foxieproducts/cardclock/firmware/src/characters.hpp

// This file implements characters as lines of code within display.hpp
// It is not meant to be included elsewhere.

// clang-format off
#define CHAR(c, ...) (character == c) { charData = { __VA_ARGS__ }; }
if      CHAR('A',
          0, 1, 0,
          1, 0, 1,
          1, 0, 1,
          1, 1, 1,
          1, 0, 1)
else if CHAR('B',
          1, 1, 0,
          1, 0, 1,
          1, 1, 0,
          1, 0, 1,
          1, 1, 0)
else if CHAR('C',
          0, 1, 1,
          1, 0, 0,
          1, 0, 0,
          1, 0, 0,
          0, 1, 1)
else if CHAR('D',
          1, 1, 0,
          1, 0, 1,
          1, 0, 1,
          1, 0, 1,
          1, 1, 0)
else if CHAR('E',
          1, 1, 1,
          1, 0, 0,
          1, 1, 1,
          1, 0, 0,
          1, 1, 1)
else if CHAR('F',
          1, 1, 1,
          1, 0, 0,
          1, 1, 1,
          1, 0, 0,
          1, 0, 0)
else if CHAR('G',
          0, 1, 1,
          1, 0, 0,
          1, 1, 1,
          1, 0, 1,
          0, 1, 1)
else if CHAR('H',
          1, 0, 1,
          1, 0, 1,
          1, 1, 1,
          1, 0, 1,
          1, 0, 1)
else if CHAR('I',
          1,
          1,
          1,
          1,
          1)
else if CHAR('J',
          0, 0, 1,
          0, 0, 1,
          0, 0, 1,
          0, 0, 1,
          1, 1, 0)
else if CHAR('K',
          1, 0, 1,
          1, 0, 1,
          1, 1, 0,
          1, 0, 1,
          1, 0, 1)
else if CHAR('L',
          1, 0, 0,
          1, 0, 0,
          1, 0, 0,
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
          1, 1, 1,
          0, 1, 0)
else if CHAR(CHAR_RIGHT_ARROW,
          0, 0, 0,
          0, 1, 0,
          0, 1, 1,
          0, 1, 0,
          0, 0, 0)
else if CHAR(CHAR_LEFT_ARROW,
          0, 0, 0,
          0, 1, 0,
          1, 1, 0,
          0, 1, 0,
          0, 0, 0)
