foxieproducts/cardclock/firmware/src/option.hpp

#pragma once
#include <Arduino.h>
#include <functional>  // for std::function
#include <vector>      // for std::vector

#include "display.hpp"
#include "settings.hpp"

class Option {
  protected:
    const String m_name;
    bool m_isDone{false};
    std::function<void()> m_finishFunc;

  public:
    Option(const String& name, std::function<void()> finishFunc)
        : m_name(name), m_finishFunc(finishFunc) {}
    virtual String GetName() { return m_name; }
    virtual String GetCurrentValue() { return ""; };
    virtual void Begin(){};  // called by MenuManager on appearance
    virtual void Update() {}
    virtual void Up() {}
    virtual void Down() {}
    virtual void Finish() {  // called by MenuManager when exiting
        End();
        if (m_finishFunc) {
            m_finishFunc();
        }
    }
    virtual void End() {}

    virtual bool IsDone() { return m_isDone; }
};

class TextListOption : public Option {
  protected:
    Display& m_display;
    Settings& m_settings;
    const std::vector<String> m_values;
    int m_index{0};

  public:
    TextListOption(Display& display,
                   Settings& settings,
                   const String& name,
                   std::vector<String> values,
                   std::function<void()> finishFunc)
        : Option(name, finishFunc),
          m_display(display),
          m_settings(settings),
          m_values(values) {}

    virtual String GetCurrentValue() override {
        return m_values.size() ? m_values[m_index] : "";
    }

    virtual void Begin() override {
        if (m_values.empty()) {
            return;
        }

        if (m_values[m_index] != m_settings[m_name]) {
            // when we come back into the menu, make sure that the setting
            // selected is what is actually set in m_settings
            m_index = 0;
            for (size_t i = 0; i < m_values.size(); ++i) {
                if (m_values[i] == m_settings[m_name]) {
                    m_index = i;
                    break;
                }
            }
        }
    }

    virtual void Update() override {
        if (m_values.empty()) {
            return;
        }

        m_display.DrawText(0, m_values[m_index], GRAY);
        DrawArrows(0, m_values.size());
    }

    virtual void Up() override {
        if (m_values.empty()) {
            return;
        }

        if ((size_t)m_index < m_values.size() - 1) {
            m_index++;
            m_display.ScrollVertical(HEIGHT, 1);
        }
    }
    virtual void Down() override {
        if (m_values.empty()) {
            return;
        }

        if (m_index > 0) {
            m_index--;
            m_display.ScrollVertical(HEIGHT, -1);
        }
    }

    virtual void End() override {
        if (m_values.size()) {
            ChangeSettingToCurrentValue();
            m_settings.Save();
        }
    }

  protected:
    virtual void DrawArrows(const int min, const int max) {
        const int downColor = m_index > min ? GREEN : DARK_GREEN;
        const int upColor = m_index < max - 1 ? GREEN : DARK_GREEN;

        m_display.DrawChar(14, CHAR_UP_ARROW, upColor);
        m_display.DrawChar(14, CHAR_DOWN_ARROW, downColor);
    }
    virtual void ChangeSettingToCurrentValue() {
        m_settings[GetName()] = GetCurrentValue();
    }
};

class RangeOption : public TextListOption {
  protected:
    int m_min{0};
    int m_max{0};

  public:
    RangeOption(Display& display,
                Settings& settings,
                String name,
                const int min,
                const int max,
                std::function<void()> finishFunc)
        : TextListOption(display, settings, name, {}, finishFunc),
          m_min(min),
          m_max(max) {}
    virtual String GetCurrentValue() override { return String(m_index); }

    virtual void Begin() override {
        if (m_index != m_settings[m_name].as<int>()) {
            // when we come back into the menu, make sure that the setting
            // selected is what is actually set in m_settings
            m_index = m_settings[m_name].as<int>();
        }
    }

    virtual void Update() override {
        m_display.DrawText(0, String(m_index), GRAY);
        DrawArrows(m_min, m_max);
    }

    virtual void Up() override {
        if (m_index < m_max) {
            m_index++;
            ChangeSettingToCurrentValue();
        }
    }
    virtual void Down() override {
        if (m_index > m_min) {
            m_index--;
            ChangeSettingToCurrentValue();
        }
    }

    virtual void End() override {
        ChangeSettingToCurrentValue();
        m_settings.Save();
    }
};

class OneShotOption : public Option {
  private:
    std::function<void()> m_runFuncOnce;

  public:
    OneShotOption(String name,
                  std::function<void()> runFuncOnce,
                  std::function<void()> finishFunc)
        : Option(name, finishFunc), m_runFuncOnce(runFuncOnce) {}

    virtual void Begin() override {
        m_runFuncOnce();
        m_isDone = true;
    }
};
